bmink/Dominos_House_Plans/Views/View 02.png

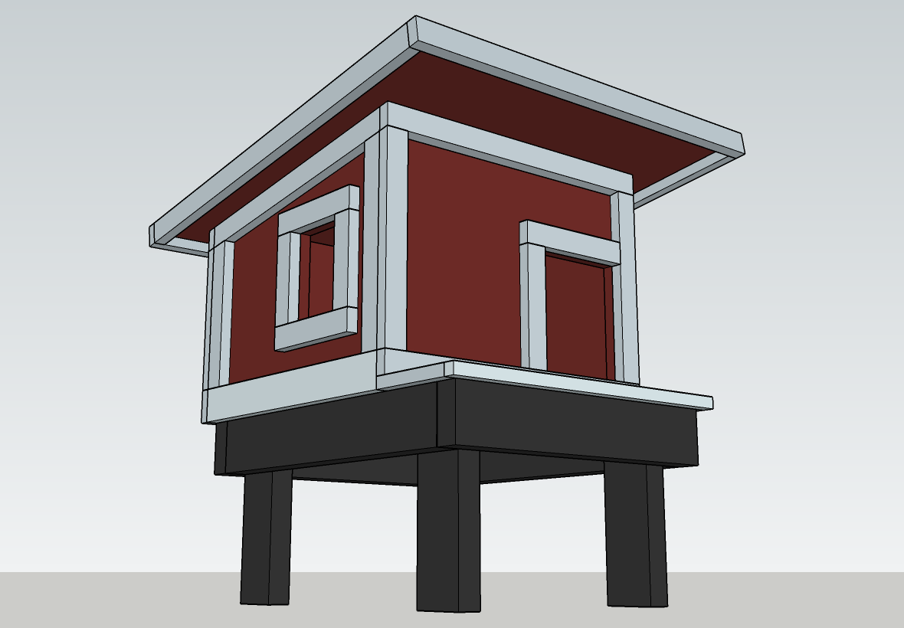
Views/View 02.png
