bmink/Dominos_House_Plans/Views/View 03.png

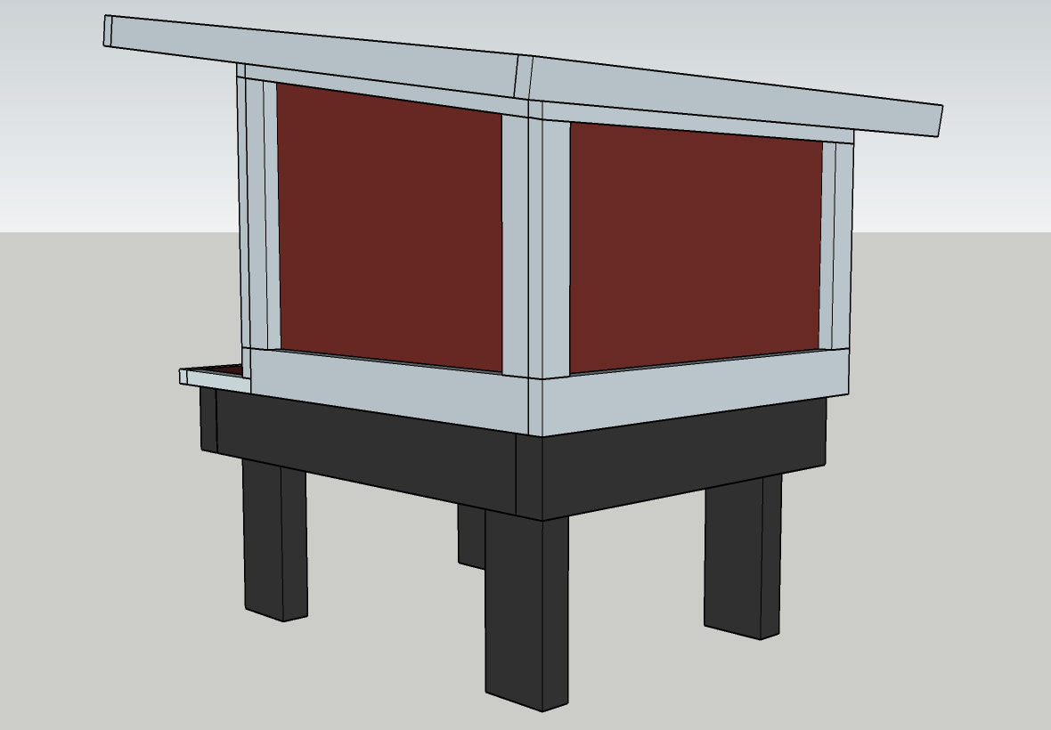
Views/View 03.png
