bmink/Dominos_House_Plans/Views/View 09.png

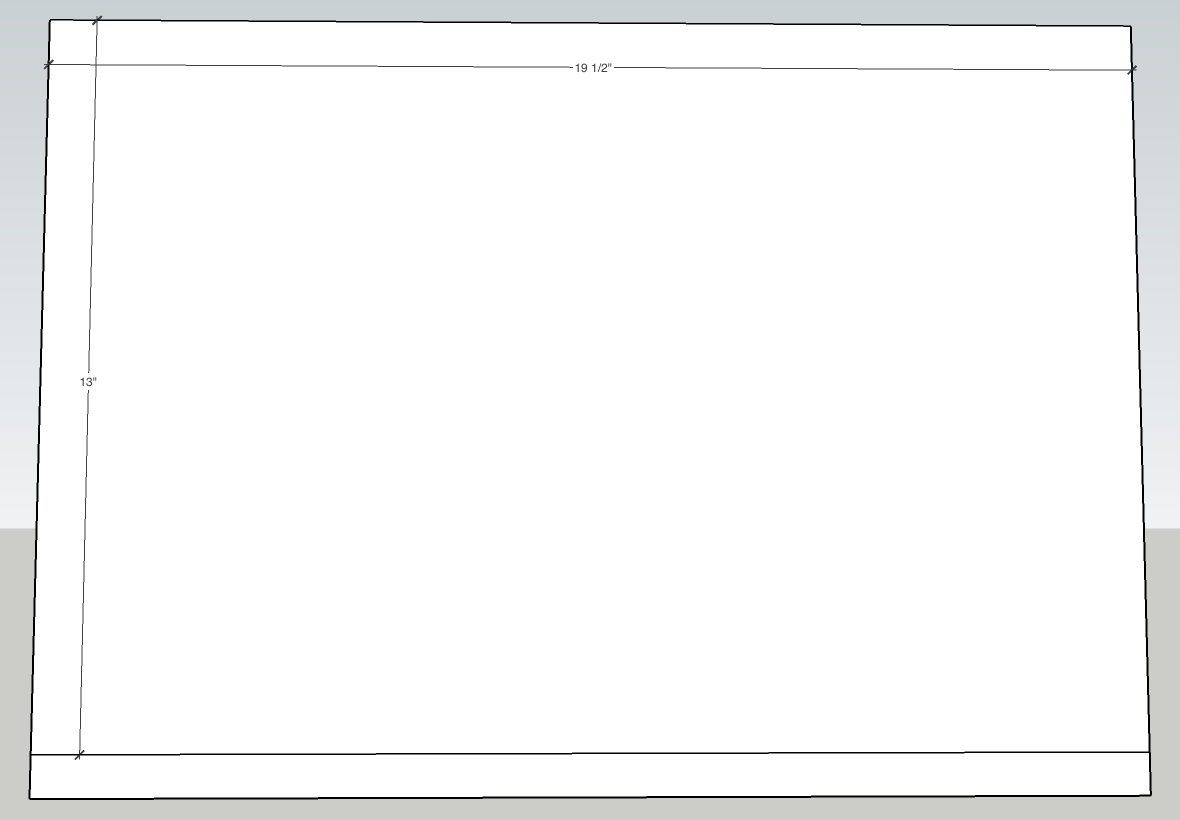
Views/View 09.png
