bmink/Dominos_House_Plans/Views/View 10.png

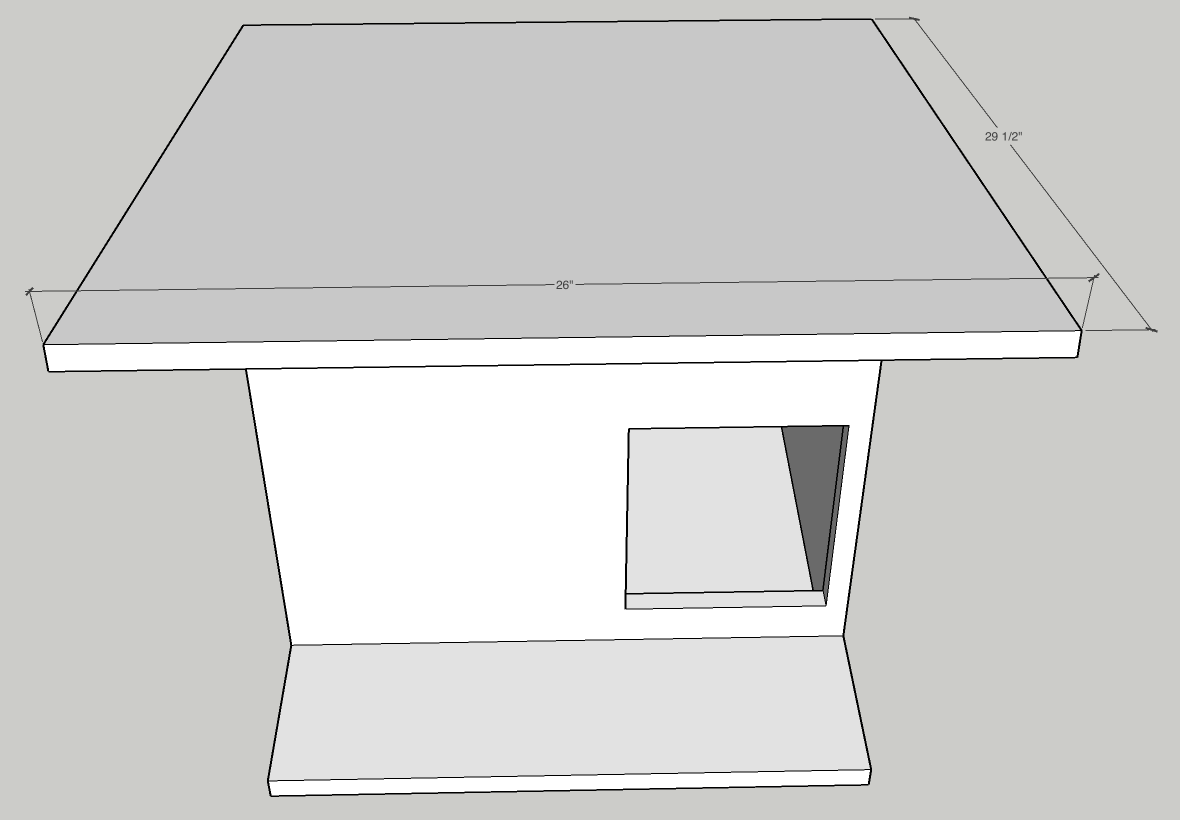
Views/View 10.png
