bmink/Dominos_House_Plans/Views/View 11.png

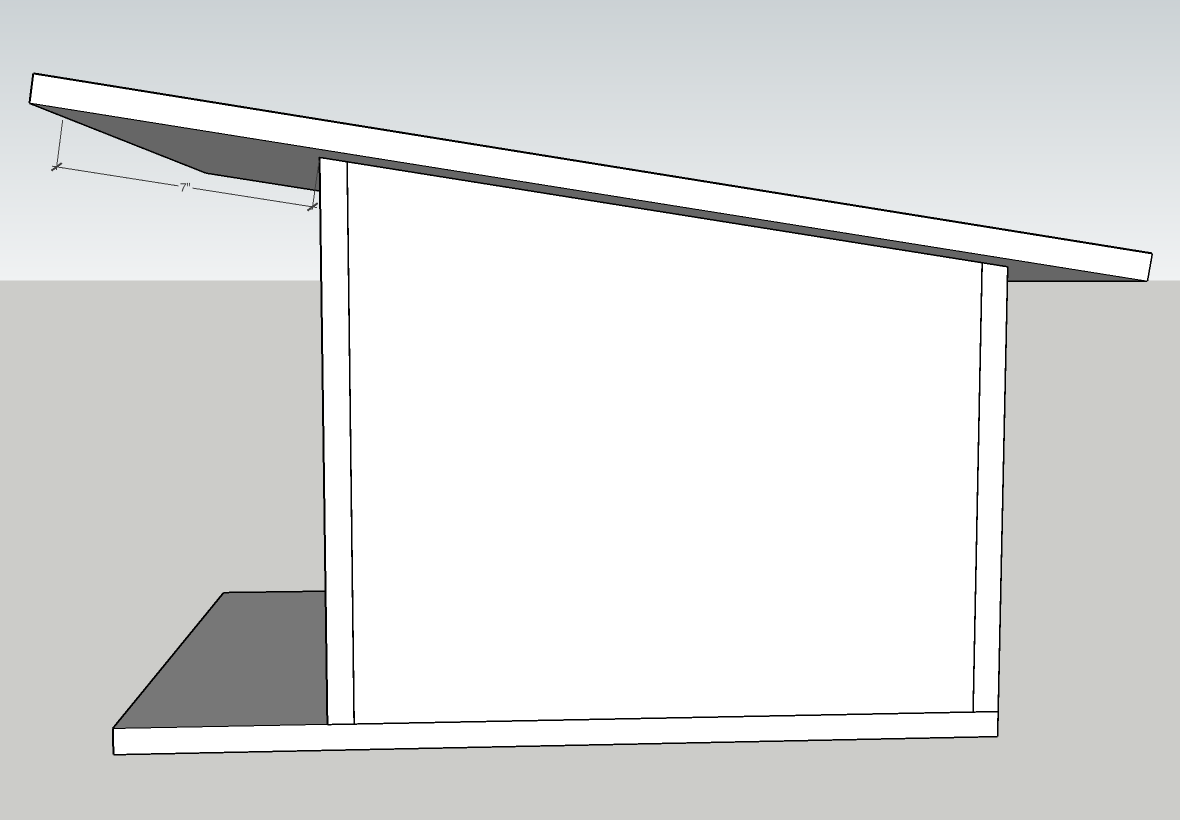
Views/View 11.png
