bmink/Dominos_House_Plans/Views/View 12.png

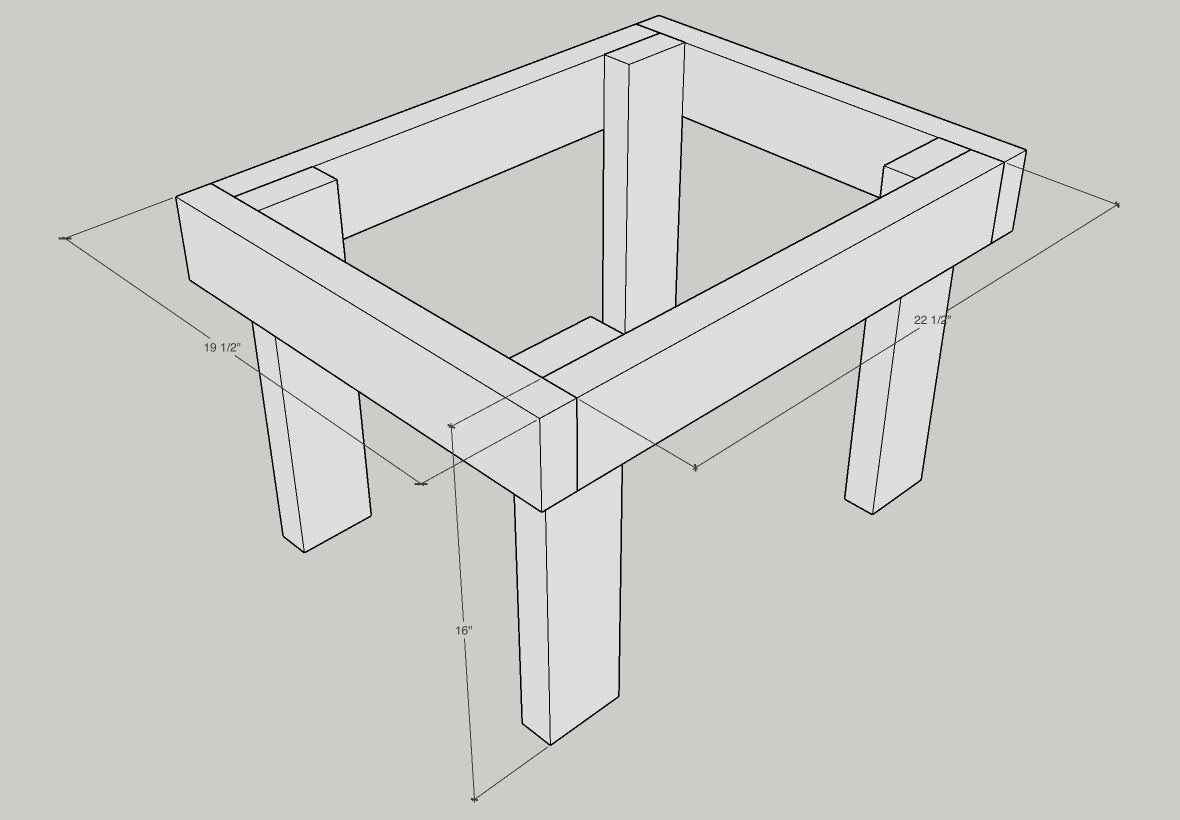
Views/View 12.png
